ageppert/Core-64c-Compact-Interactive-Core-Memory-Badge/Electronics/Core64c LB V0.4 KiCAD 5/Core64c LB v0.4 Render Bottom.png

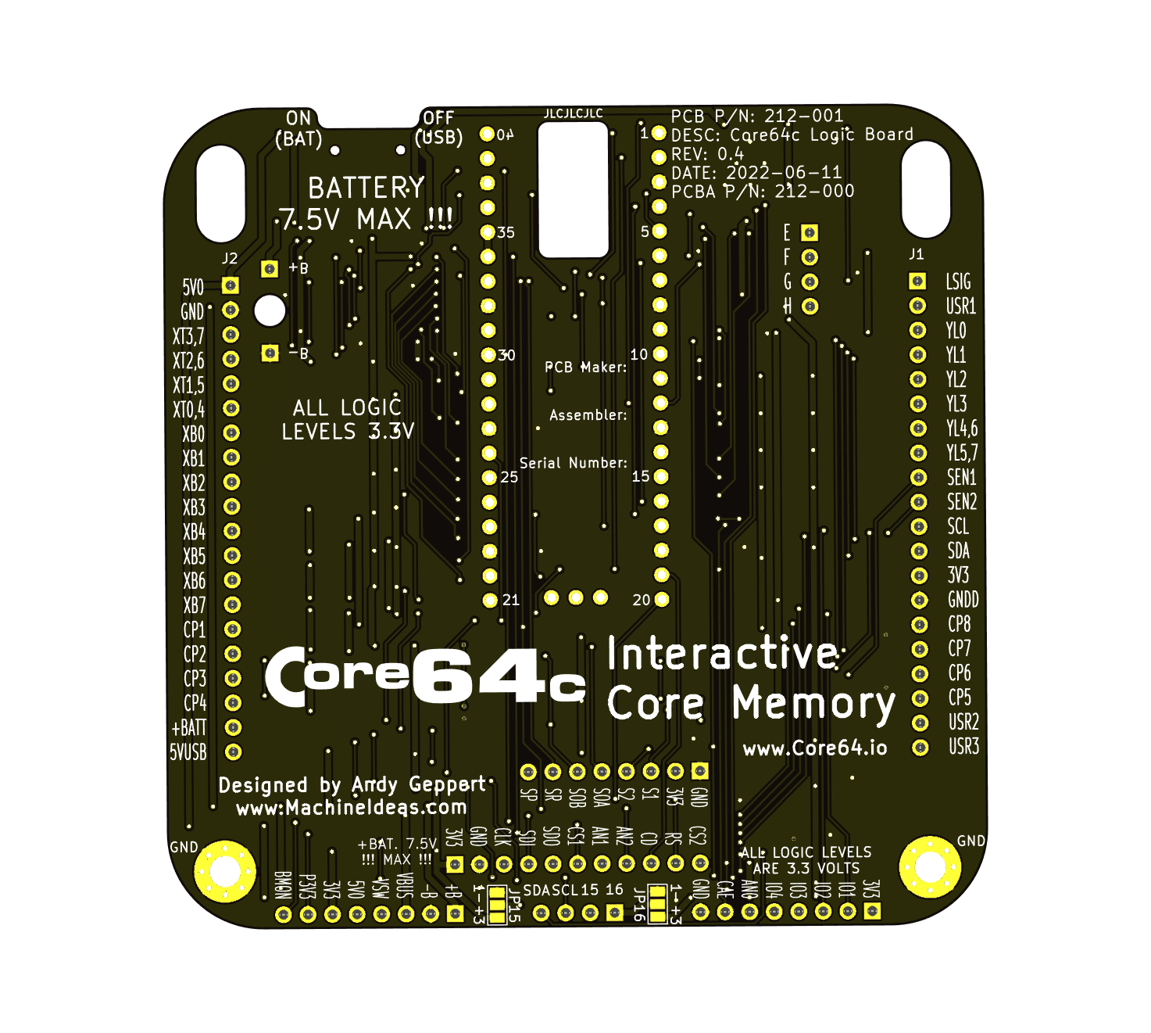
Electronics/Core64c LB V0.4 KiCAD 5/Core64c LB v0.4 Render Bottom.png
