ageppert/Core-64c-Compact-Interactive-Core-Memory-Badge/Electronics/Core64c LB V0.4 KiCAD 5/Core64c Production File Review/jlcS2K58HEJHQ69bottom-4480x3200.png

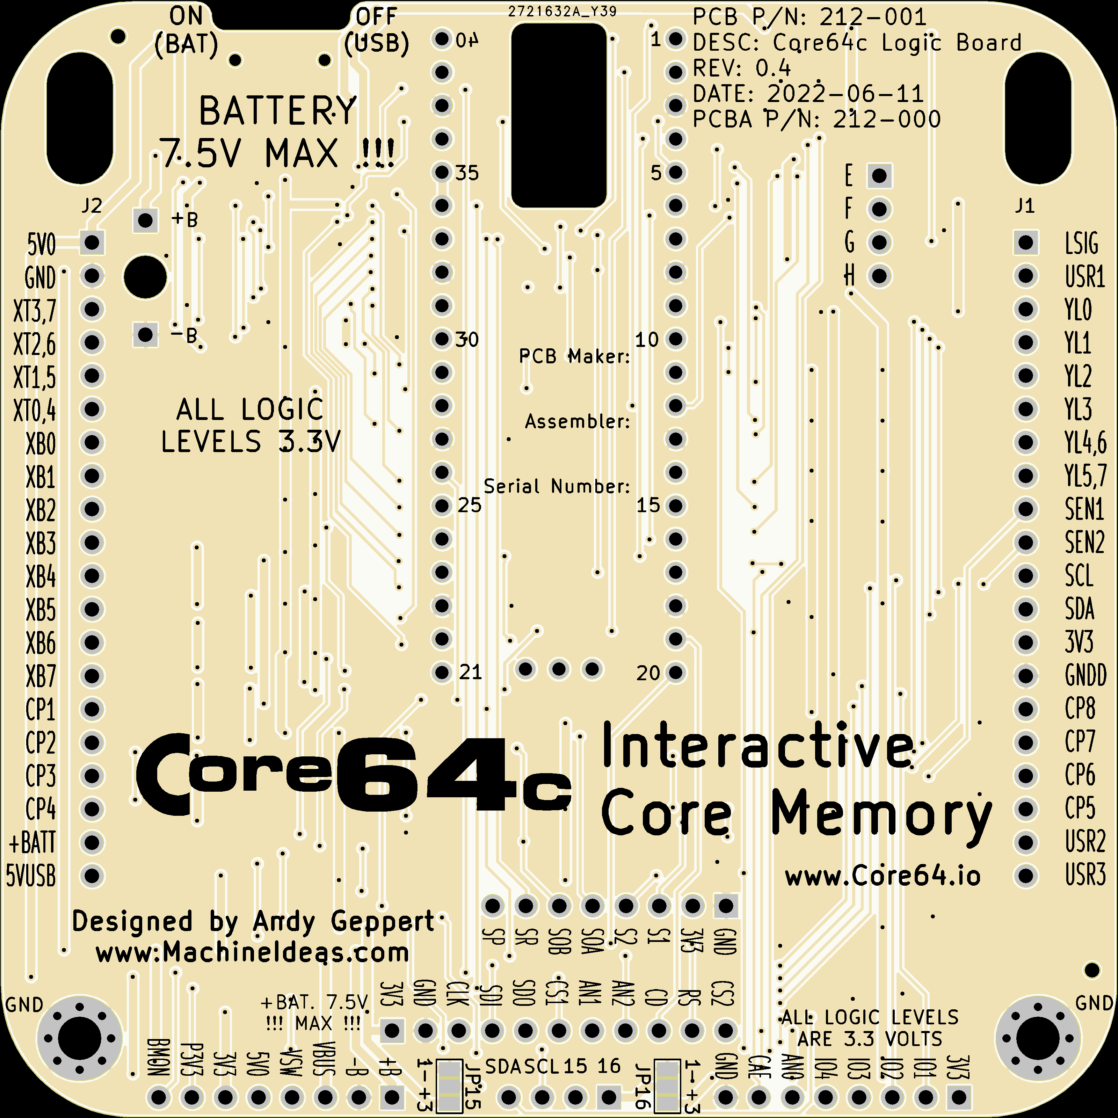
Electronics/Core64c LB V0.4 KiCAD 5/Core64c Production File Review/jlcS2K58HEJHQ69bottom-4480x3200.png
