ageppert/Core-64c-Compact-Interactive-Core-Memory-Badge/Electronics/Core64c LB V0.5 Schematic and Renders/Render Core64c LB V0.5 Front.png

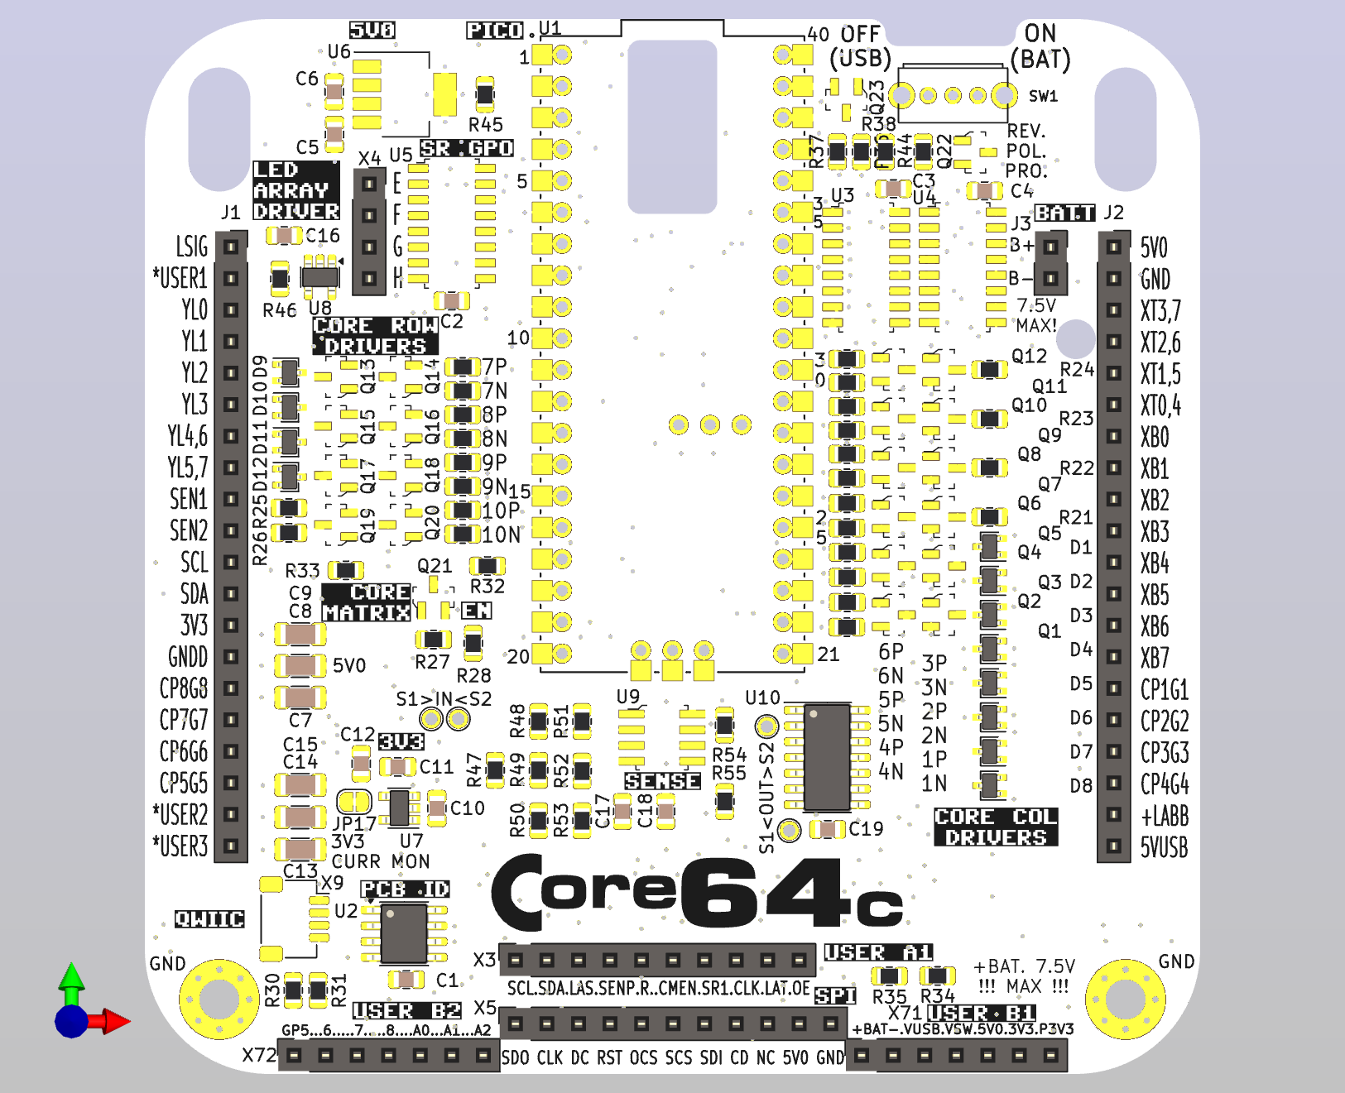
Electronics/Core64c LB V0.5 Schematic and Renders/Render Core64c LB V0.5 Front.png
