ageppert/Core-64c-Compact-Interactive-Core-Memory-Badge/Electronics/Core64c LB V0.6-V0.7 Schematic and Renders/Render Core64c LB V0.6-V0.7 Back.png

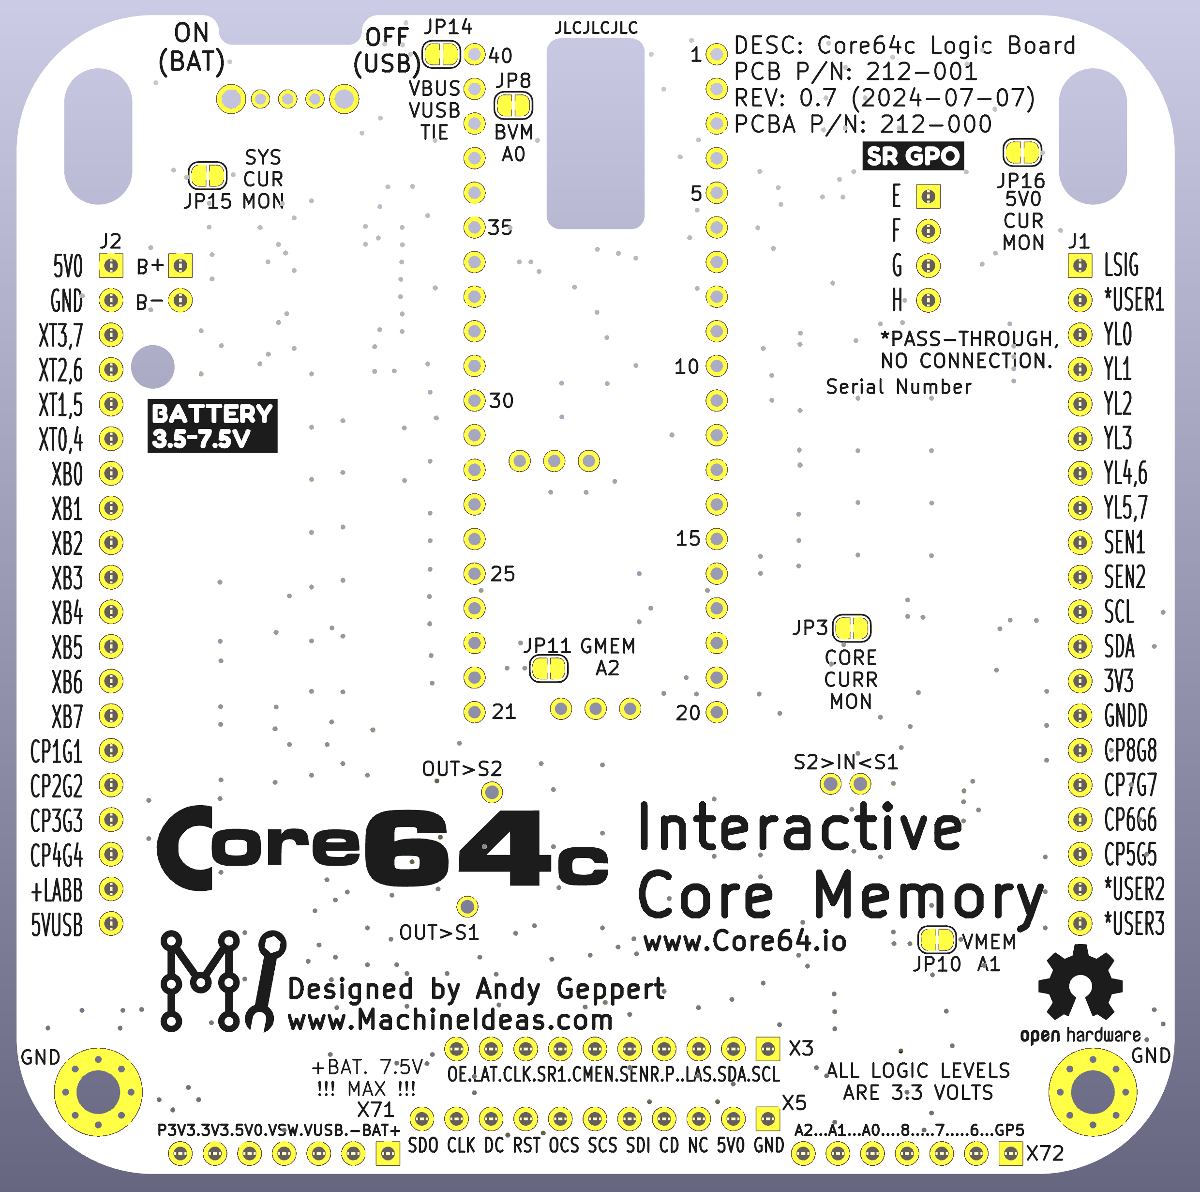
Electronics/Core64c LB V0.6-V0.7 Schematic and Renders/Render Core64c LB V0.6-V0.7 Back.png
