ageppert/Core-64c-Compact-Interactive-Core-Memory-Badge/Electronics/Core64c LB V0.3/Core64c LB V0.3 2022-05-17 Gerbers/JLCPCB LCSC Components List.png

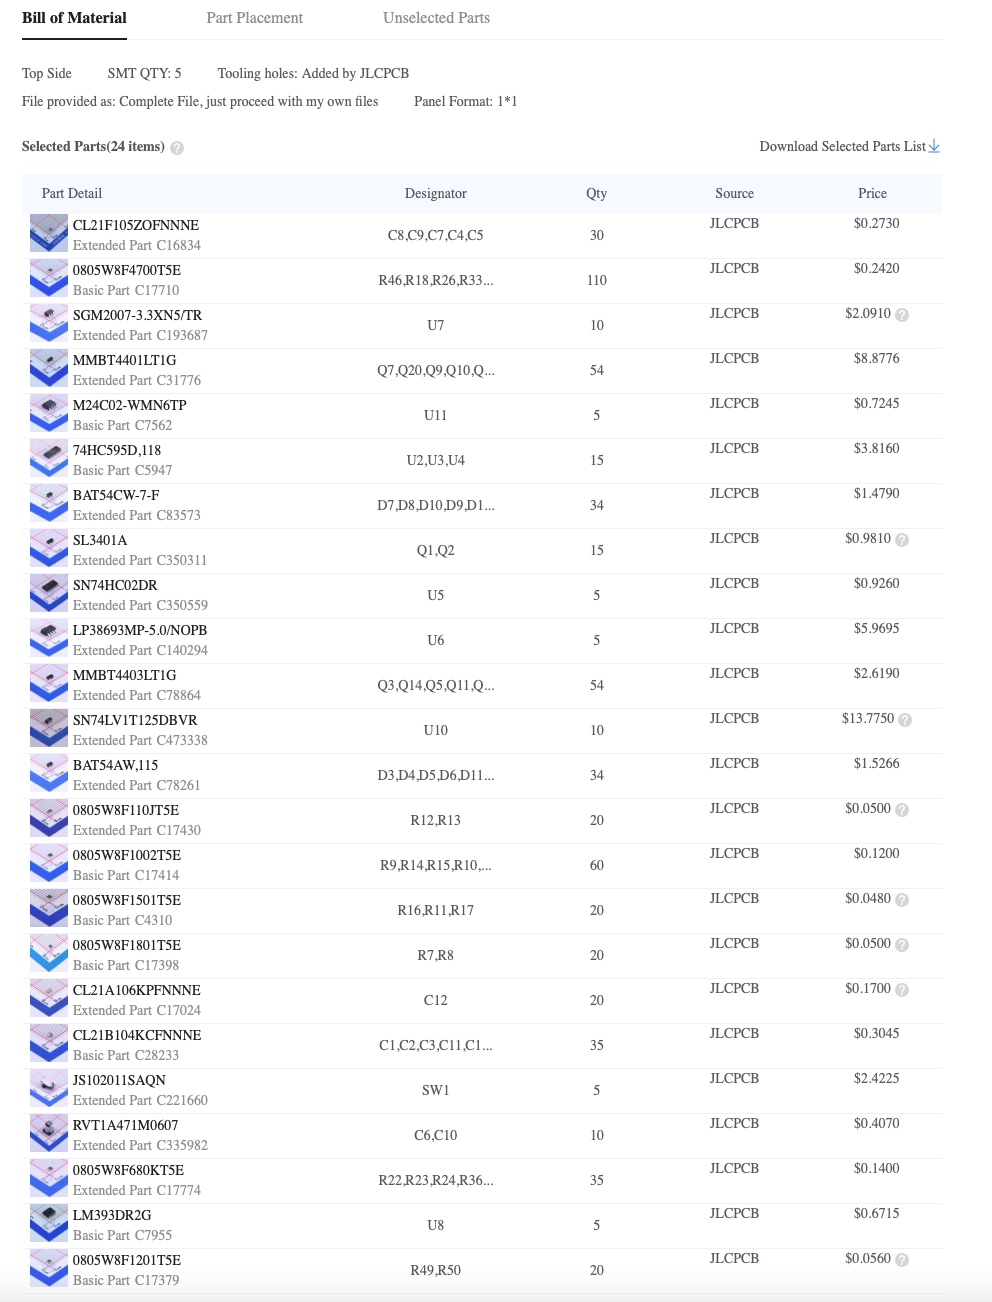
Electronics/Core64c LB V0.3/Core64c LB V0.3 2022-05-17 Gerbers/JLCPCB LCSC Components List.png
