ageppert/Core-64c-Compact-Interactive-Core-Memory-Badge/Electronics/Core64c LB V0.5 Manufacturing/Core64c LB v0.5 2024-03-24 (Qty10) Gerbers/1938282352640-Produce_DanZhi.SMT_Snapshot.Top.2721632A_Y48.SMT02403251663324.png

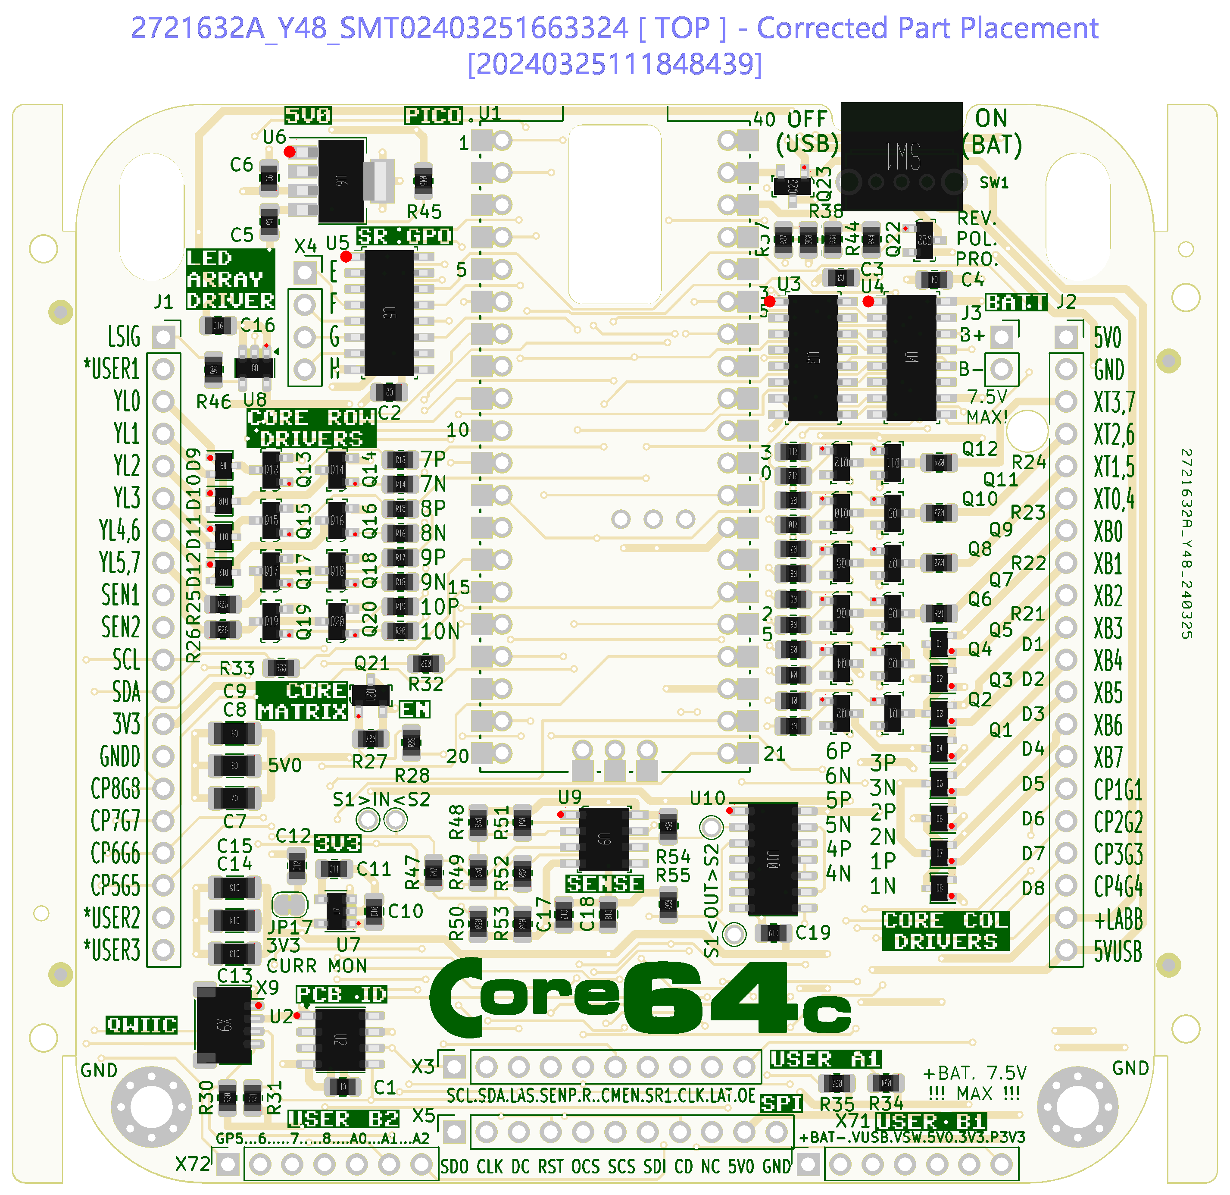
Electronics/Core64c LB V0.5 Manufacturing/Core64c LB v0.5 2024-03-24 (Qty10) Gerbers/1938282352640-Produce_DanZhi.SMT_Snapshot.Top.2721632A_Y48.SMT02403251663324.png
